wh201906/PM3-Modding/PM3_USB2TCP/firmware/main/wifi/wifi_station.c

#include <string.h>
#include "freertos/FreeRTOS.h"
#include "freertos/task.h"
#include "freertos/event_groups.h"
#include "esp_system.h"
#include "esp_event.h"
#include "esp_log.h"

#include <netdb.h>
#include "lwip/err.h"
#include "lwip/sys.h"

#include "wifi.h"

/* FreeRTOS event group to signal when we are connected*/
static EventGroupHandle_t s_wifi_sta_event_group;

/* The event group allows multiple bits for each event, but we only care about two events:
 * - we are connected to the AP with an IP
 * - we failed to connect after the maximum amount of retries */
#define WIFI_STA_CONNECTED_BIT BIT0
#define WIFI_STA_FAIL_BIT      BIT1

static int s_retry_num = 0;
static esp_netif_t *netif_wifi_sta = NULL;

static void wifi_sta_set_static_ip(esp_netif_t *netif)
{
    if (esp_netif_dhcpc_stop(netif) != ESP_OK) {
        ESP_LOGE(TAG_WIFI, "Failed to stop DHCP client");
        return;
    }
    esp_netif_ip_info_t ip;
    memset(&ip, 0 , sizeof(esp_netif_ip_info_t));
    ip.ip.addr = ipaddr_addr(WIFI_STA_STATIC_IP_ADDR);
    ip.netmask.addr = ipaddr_addr(WIFI_STA_STATIC_NETMASK_ADDR);
    ip.gw.addr = ipaddr_addr(WIFI_STA_STATIC_GATEWAY_ADDR);
    if (esp_netif_set_ip_info(netif, &ip) != ESP_OK) {
        ESP_LOGE(TAG_WIFI, "Failed to set IP info");
        return;
    }
    ESP_LOGD(TAG_WIFI, "Success to set static ip: %s, netmask: %s, gw: %s", WIFI_STA_STATIC_IP_ADDR, WIFI_STA_STATIC_NETMASK_ADDR, WIFI_STA_STATIC_GATEWAY_ADDR);
}

static void wifi_sta_event_handler(void* arg, esp_event_base_t event_base, int32_t event_id, void* event_data)
{
    if (event_base == WIFI_EVENT && event_id == WIFI_EVENT_STA_START) {
        s_retry_num = 0;
        esp_wifi_connect();
    } else if (event_base == WIFI_EVENT && event_id == WIFI_EVENT_STA_CONNECTED) {
        ;
#ifdef WIFI_STA_STATIC_IP_ADDR
        if (strlen(WIFI_STA_STATIC_IP_ADDR) > 0) {
            wifi_sta_set_static_ip(netif_wifi_sta);
        }
#endif
    } else if (event_base == WIFI_EVENT && event_id == WIFI_EVENT_STA_DISCONNECTED) {
        if (s_retry_num < WIFI_STA_MAX_RETRY) {
            esp_wifi_connect();
            s_retry_num++;
            ESP_LOGI(TAG_WIFI, "retry to connect to the AP");
        } else {
            xEventGroupSetBits(s_wifi_sta_event_group, WIFI_STA_FAIL_BIT);
        }
        ESP_LOGI(TAG_WIFI,"connect to the AP fail");
    } else if (event_base == IP_EVENT && event_id == IP_EVENT_STA_GOT_IP) {
        ip_event_got_ip_t* event = (ip_event_got_ip_t*) event_data;
        ESP_LOGI(TAG_WIFI, "got ip:" IPSTR, IP2STR(&event->ip_info.ip));
        s_retry_num = 0;
        xEventGroupSetBits(s_wifi_sta_event_group, WIFI_STA_CONNECTED_BIT);
    }
}

void wifi_init_sta(void)
{
    s_wifi_sta_event_group = xEventGroupCreate();

    netif_wifi_sta = esp_netif_create_default_wifi_sta();

    wifi_init_config_t cfg = WIFI_INIT_CONFIG_DEFAULT();
    ESP_ERROR_CHECK(esp_wifi_init(&cfg));

    esp_event_handler_instance_t instance_any_id;
    esp_event_handler_instance_t instance_got_ip;
    ESP_ERROR_CHECK(esp_event_handler_instance_register(WIFI_EVENT, ESP_EVENT_ANY_ID, &wifi_sta_event_handler, NULL, &instance_any_id));
    ESP_ERROR_CHECK(esp_event_handler_instance_register(IP_EVENT, IP_EVENT_STA_GOT_IP, &wifi_sta_event_handler, NULL, &instance_got_ip));

    wifi_config_t wifi_config = {
        .sta = {
            .ssid = WIFI_SSID,
            .password = WIFI_PWD,
            .threshold.authmode = WIFI_AUTH_OPEN, // weakest authmode to accept
            .sae_pwe_h2e = WPA3_SAE_PWE_BOTH,
            .sae_h2e_identifier = WIFI_STA_H2E_IDENTIFIER,
        },
    };
    ESP_ERROR_CHECK(esp_wifi_set_mode(WIFI_MODE_STA));
    ESP_ERROR_CHECK(esp_wifi_set_config(WIFI_IF_STA, &wifi_config));
    ESP_ERROR_CHECK(esp_wifi_start());

    ESP_LOGI(TAG_WIFI, "wifi_init_sta finished.");

    /* Waiting until either the connection is established (WIFI_STA_CONNECTED_BIT) or connection failed for the maximum
     * number of re-tries (WIFI_STA_FAIL_BIT). The bits are set by wifi_sta_event_handler() (see above) */
    EventBits_t bits = xEventGroupWaitBits(s_wifi_sta_event_group,
            WIFI_STA_CONNECTED_BIT | WIFI_STA_FAIL_BIT,
            pdFALSE,
            pdFALSE,
            portMAX_DELAY);

    /* xEventGroupWaitBits() returns the bits before the call returned, hence we can test which event actually
     * happened. */
    if (bits & WIFI_STA_CONNECTED_BIT) {
        ESP_LOGI(TAG_WIFI, "connected to ap SSID:%s password:%s", WIFI_SSID, WIFI_PWD);
    } else if (bits & WIFI_STA_FAIL_BIT) {
        ESP_LOGI(TAG_WIFI, "Failed to connect to SSID:%s, password:%s", WIFI_SSID, WIFI_PWD);
    } else {
        ESP_LOGE(TAG_WIFI, "UNEXPECTED EVENT");
    }
}
