wh201906/PM3-Modding/PM3_USB2TCP/firmware/main/wifi/wifi_ap.c

#include <string.h>
#include "freertos/FreeRTOS.h"
#include "freertos/task.h"
#include "esp_mac.h"
#include "esp_event.h"
#include "esp_log.h"

#include "lwip/err.h"
#include "lwip/sys.h"

#include "wifi.h"

static void wifi_ap_event_handler(void *arg, esp_event_base_t event_base, int32_t event_id, void *event_data)
{
    if (event_id == WIFI_EVENT_AP_STACONNECTED)
    {
        wifi_event_ap_staconnected_t *event = (wifi_event_ap_staconnected_t *)event_data;
        ESP_LOGI(TAG_WIFI, "station " MACSTR " join, AID=%d", MAC2STR(event->mac), event->aid);
    }
    else if (event_id == WIFI_EVENT_AP_STADISCONNECTED)
    {
        wifi_event_ap_stadisconnected_t *event = (wifi_event_ap_stadisconnected_t *)event_data;
        ESP_LOGI(TAG_WIFI, "station " MACSTR " leave, AID=%d", MAC2STR(event->mac), event->aid);
    }
}

void wifi_init_softap(void)
{
    esp_netif_create_default_wifi_ap();

    wifi_init_config_t cfg = WIFI_INIT_CONFIG_DEFAULT();
    ESP_ERROR_CHECK(esp_wifi_init(&cfg));

    ESP_ERROR_CHECK(esp_event_handler_instance_register(WIFI_EVENT, ESP_EVENT_ANY_ID, &wifi_ap_event_handler, NULL, NULL));

    wifi_config_t wifi_config = {
        .ap = {
            .ssid = WIFI_SSID,
            .ssid_len = strlen(WIFI_SSID),
            .channel = WIFI_AP_CHANNEL,
            .password = WIFI_PWD,
            .max_connection = WIFI_AP_MAX_STA_CONN,
            .authmode = WIFI_AUTH_WPA2_PSK,
            .pmf_cfg = {
                .required = true,
            },
        },
    };
    if (strlen(WIFI_PWD) == 0)
    {
        wifi_config.ap.authmode = WIFI_AUTH_OPEN;
    }

    ESP_ERROR_CHECK(esp_wifi_set_mode(WIFI_MODE_AP));
    ESP_ERROR_CHECK(esp_wifi_set_config(WIFI_IF_AP, &wifi_config));
    ESP_ERROR_CHECK(esp_wifi_start());

    ESP_LOGI(TAG_WIFI, "wifi_init_softap finished. SSID:%s password:%s channel:%d", WIFI_SSID, WIFI_PWD, WIFI_AP_CHANNEL);
}
